FPGA-Computer/Alarm-Detection/STM32F030/Nokia5110.c

/*
  Nokia5110.c
 
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
	If not, see http://www.gnu.org/licenses/gpl-3.0.en.html
 */ 
 
#include "hardware.h"
#include "font.h"
#include "graphics.h"

uint8_t TextAttr=0, CurCol, CurRow;

const uint8_t LCD_InitCmd[]=
{ 
	LCD_CMD_FH1, LCD_Contrast|LCD_ContrastDefault, LCD_TempCtrl,
  LCD_SetBias, LCD_CMD_FH0, LCD_Disp_Off
 };

void LCD_Init(void)
{ 
  LCD_CmdMode();
  SPI_Block_Write(LCD_InitCmd,sizeof(LCD_InitCmd));

  LCD_Cls();
  SPI_ByteWrite(LCD_Disp_On);
 }

void LCD_Cord_XY(uint8_t X, uint8_t Y)
{
  LCD_CmdMode();
  SPI_ByteWrite(LCD_Addr_X | (X & 0x7f));
  SPI_ByteWrite(LCD_Addr_Y | (Y & 0x07));
 }

// Text
void LCD_Moveto(uint8_t Col, uint8_t Row)
{
  LCD_Cord_XY(CurCol=Col*LCD_SYM_WIDTH,CurRow=Row);
 }

void LCD_Cls(void)
{ 
  LCD_Cord_XY(0,0);
  LCD_DataMode();

  SPI_Block_Fill(0x0,LCD_MAX_X*LCD_MAX_Y);
  LCD_Home();
}

void Cursor_NewLine(void)
{ 
  CurCol=0;
  CurRow++;

  if(CurRow==LCD_MAXROW)
  CurRow=0;
 }

void LCD_HalfWidthCh(uint8_t Ch)
{
  SPI_Block_Write(&Font_5x8[(Ch-Font_5x8_CH_LOW)*LCD_TEXT_WIDTH+1],LCD_SYM_WIDTH/2);
 }

void LCD_PutCh(uint8_t Ch)
{ const uint8_t *ptr;
  uint8_t i, Width;

  if((Ch>=Font_5x8_CH_LOW)&&(Ch<=Font_5x8_CH_HIGH))
  { 
    LCD_DataMode();	
    ptr = &Font_5x8[(Ch-Font_5x8_CH_LOW)*LCD_TEXT_WIDTH];		// Width = 5
    Width=LCD_TEXT_WIDTH;

    if(TextAttr==TextAttr_Normal)
      SPI_Block_Write(ptr,Width);
    else if(TextAttr==TextAttr_Invert)      
      for(i=Width;i;i--)
				SPI_ByteWrite(~*ptr++);

    if(!(Ch & 0x80))
      SPI_ByteWrite((TextAttr==TextAttr_Invert)?0xff:0);

    CurCol+=LCD_SYM_WIDTH;

    // keep track of text cursor
    if(CurCol>LCD_MAX_X)
    { 
			CurCol%=LCD_MAX_X;
      Cursor_NewLine();
     }
   }
	else
		switch(Ch)
		{
			case Ch_NewLine:
				Cursor_NewLine();
				LCD_Moveto(CurCol,CurRow);
				break;
		}
 }

void LCD_Puts(const char *str)
{ 
  while (*str)
    LCD_PutCh(*str++);
 }

void Print_uint(uint16_t Value, uint16_t Div, uint8_t Format)
{
	do
  { 
    if((Format & LeadingZero)||(Value >= Div)||(Div == 1))
    { 
			Format = LeadingZero;
      LCD_PutCh('0'+Value/Div);
      Value %= Div;
     }
    else if(Format & LeftJustify)
			LCD_PutCh(' ');

    Div /= 10;
  } while(Div);
}
